trungnob/neopixel/src/patterns/pattern_102_fire_rising.cpp

// pattern_102_fire_rising.cpp
#include "../patterns.h"

// 2D Fire Rising - Disabled for now to save RAM
void pattern_fire_rising(CRGB* leds, int activeLeds, uint8_t& hue) {
  fill_solid(leds, activeLeds, CRGB::Red);
  // Placeholder
}
