trungnob/neopixel/src/patterns/pattern_117_side_fire.cpp

// pattern_117_side_fire.cpp
#include "../patterns.h"

// Side Fire - Disabled for now to save RAM
void pattern_side_fire(CRGB* leds, int activeLeds, uint8_t& hue) {
  fill_solid(leds, activeLeds, CRGB::Orange);
  // Placeholder
}
